hwoiz/ESPuino-JoliBox/Hardware-Plaforms/drill.jpg

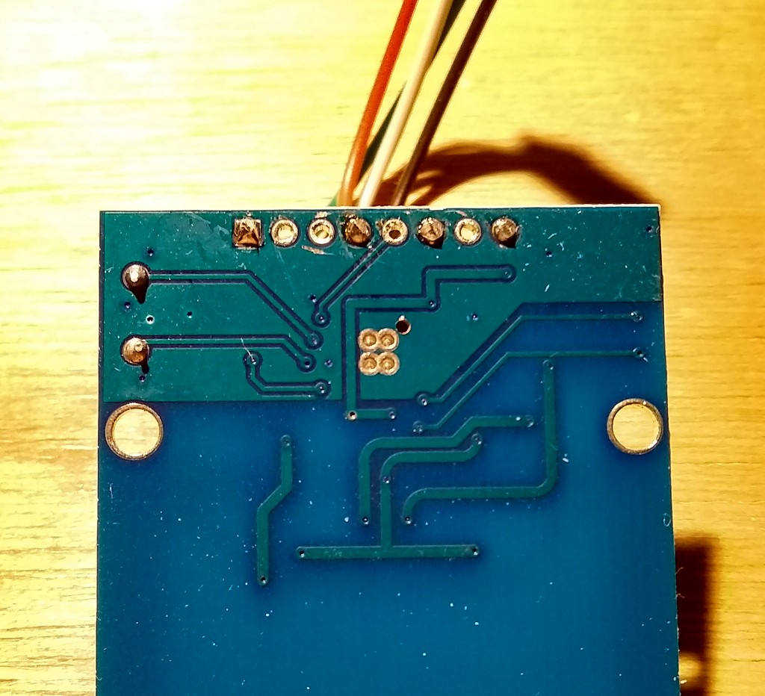
Hardware-Plaforms/drill.jpg
