hwoiz/ESPuino-JoliBox/Hardware-Plaforms/ESP32-A1S-Audiokit/docs/ESP32-A1S-Pinout.jpg

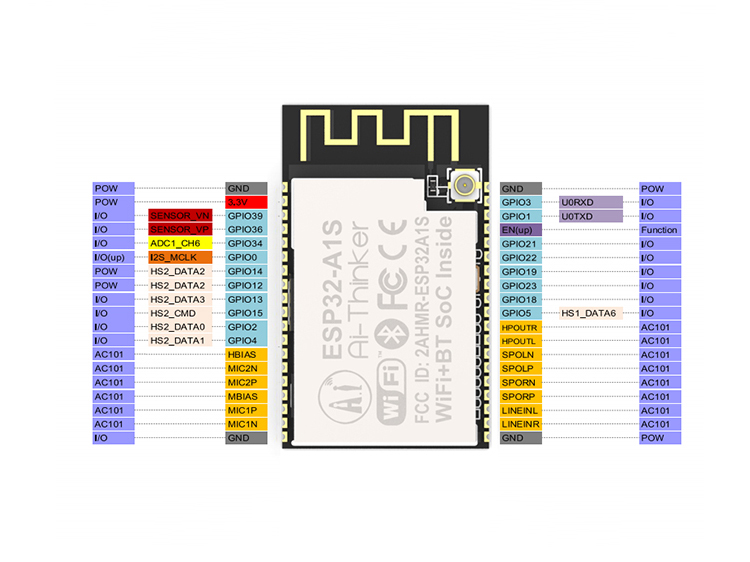
Hardware-Plaforms/ESP32-A1S-Audiokit/docs/ESP32-A1S-Pinout.jpg
