hwoiz/ESPuino-JoliBox/Hardware-Plaforms/ESP32-A1S-Audiokit/docs/ESP32-Audio-Kit2.2 ff.png

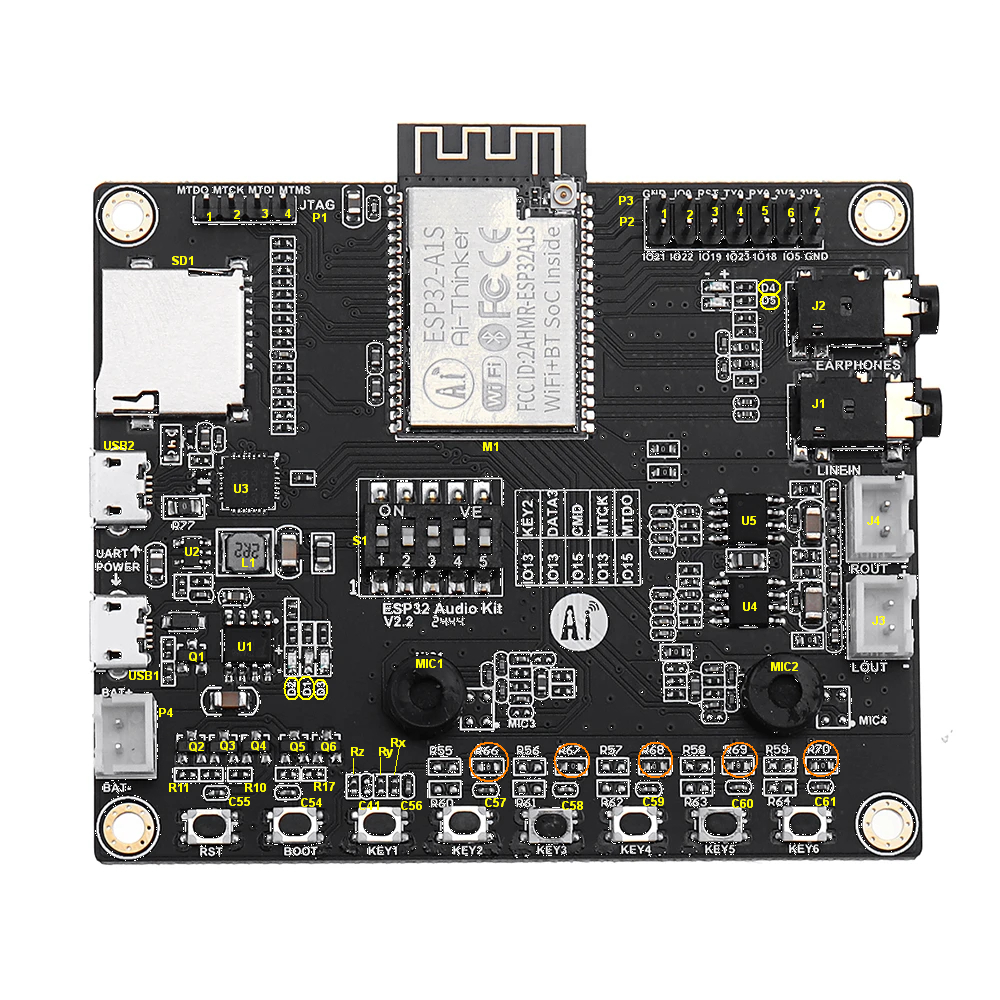
Hardware-Plaforms/ESP32-A1S-Audiokit/docs/ESP32-Audio-Kit2.2 ff.png
