hwoiz/ESPuino-JoliBox/Hardware-Plaforms/MRFC522-RC522-RFID.jpg

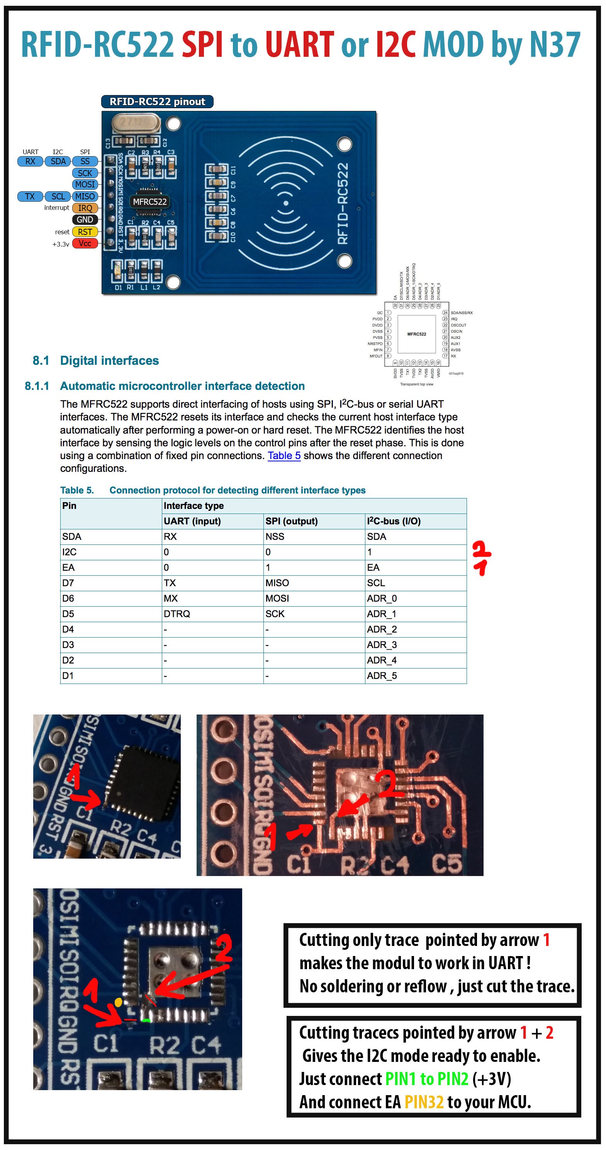
Hardware-Plaforms/MRFC522-RC522-RFID.jpg
