hwoiz/ESPuino-JoliBox/openHAB/pictures/openhab_overview.jpg

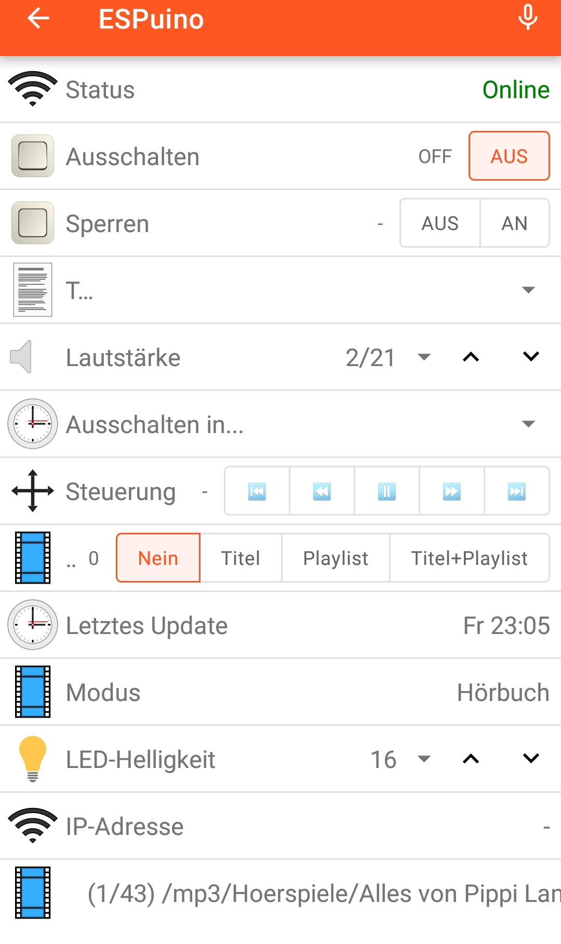
openHAB/pictures/openhab_overview.jpg
