hwoiz/ESPuino-JoliBox/openHAB/pictures/openhab_sleeping.jpg

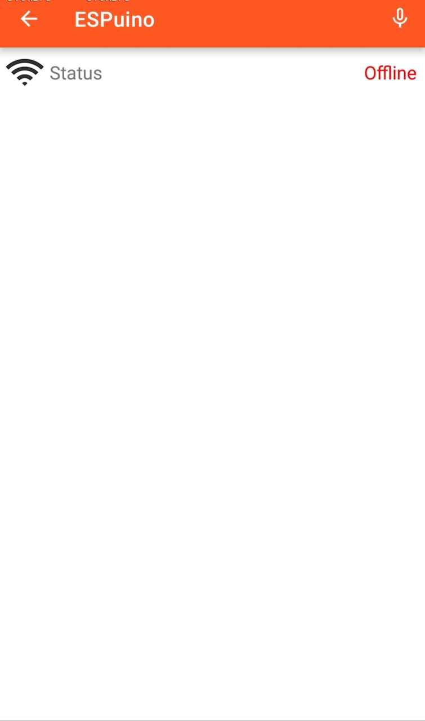
openHAB/pictures/openhab_sleeping.jpg
