hwoiz/ESPuino-JoliBox/openHAB/pictures/openhab_sleepTimer.jpg

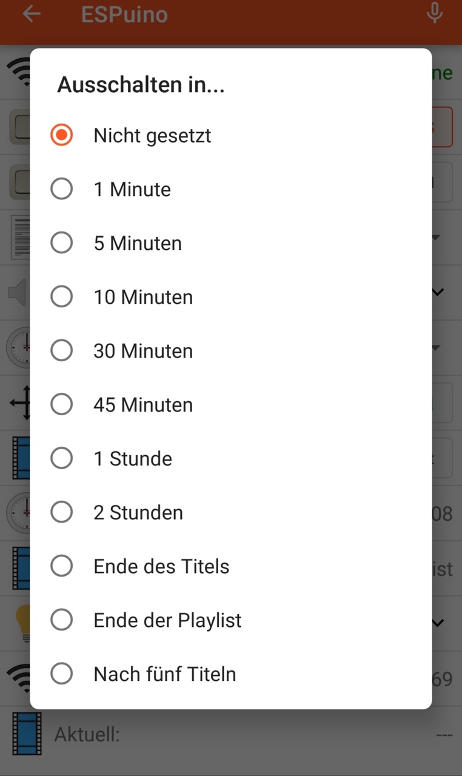
openHAB/pictures/openhab_sleepTimer.jpg
