hwoiz/ESPuino-JoliBox/openHAB/pictures/openhab_trackSelection.jpg

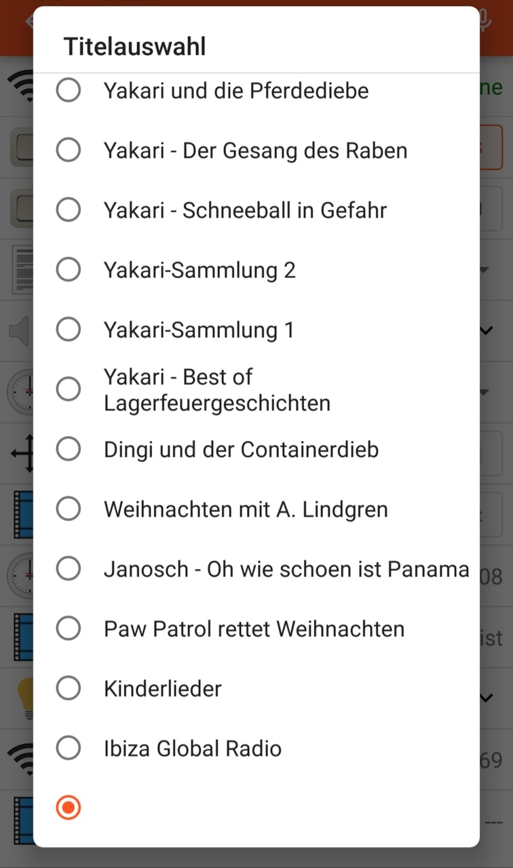
openHAB/pictures/openhab_trackSelection.jpg
