hwoiz/ESPuino-JoliBox/PCBs/AZDelivery_ESP32_NodeMCU/pictures/3d-model_front.png

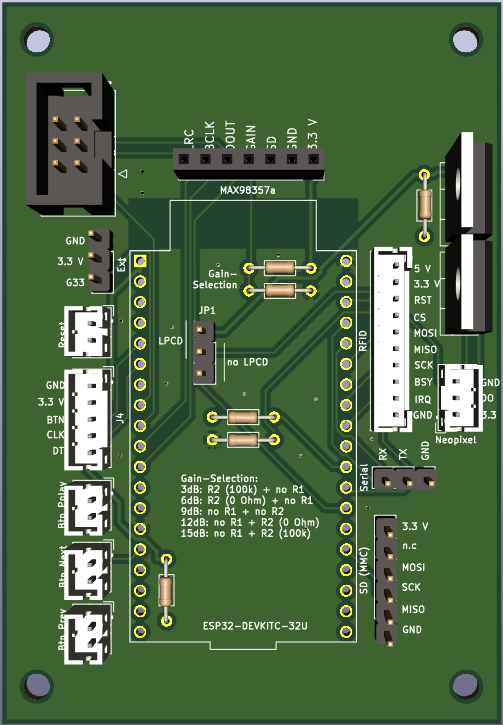
PCBs/AZDelivery_ESP32_NodeMCU/pictures/3d-model_front.png
