hwoiz/ESPuino-JoliBox/PCBs/Headphone with PCM5102a and TDA1308/Pictures/3D-model_downside.jpeg

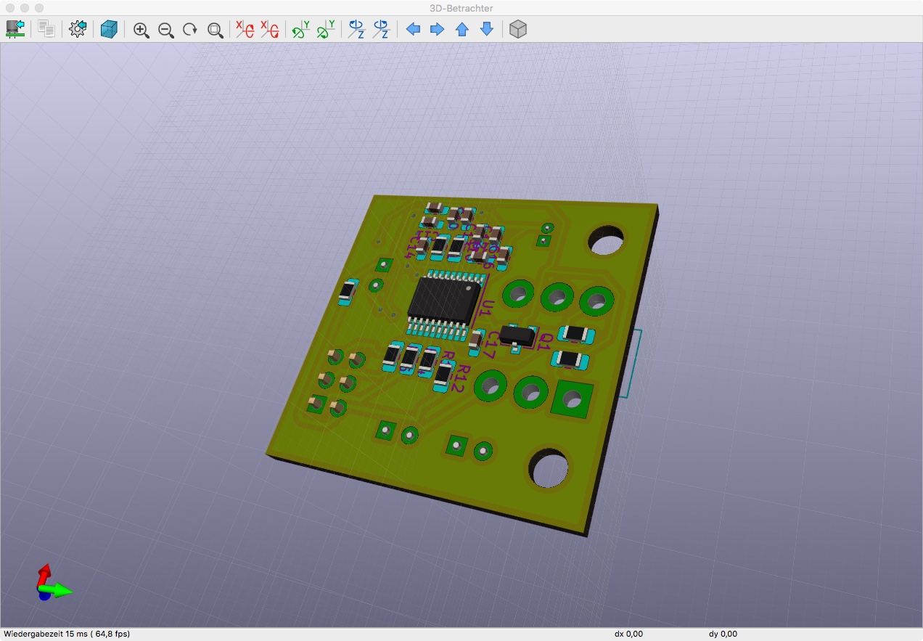
PCBs/Headphone with PCM5102a and TDA1308/Pictures/3D-model_downside.jpeg
