hwoiz/ESPuino-JoliBox/PCBs/Headphone with PCM5102a and TDA1308/Pictures/Headphone-pcb_upside.jpg

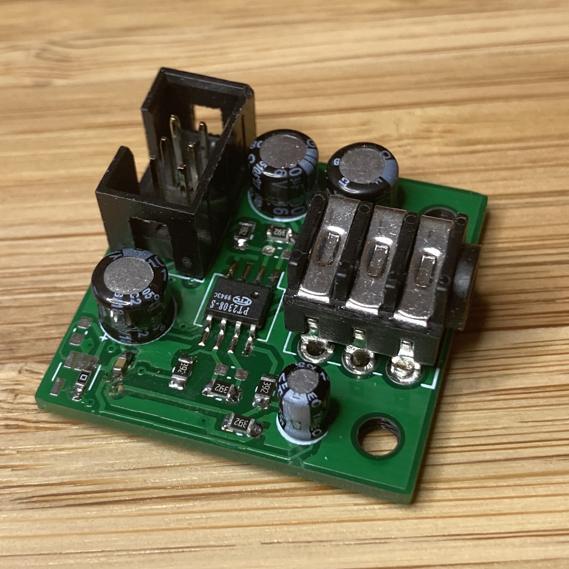
PCBs/Headphone with PCM5102a and TDA1308/Pictures/Headphone-pcb_upside.jpg
