hwoiz/ESPuino-JoliBox/PCBs/Wemos Lolin32 SD_MMC PN5180/Pictures/3d_Model_up.png

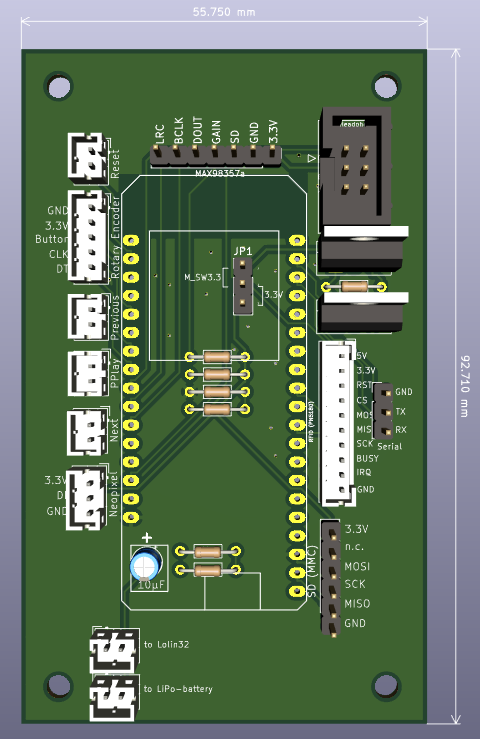
PCBs/Wemos Lolin32 SD_MMC PN5180/Pictures/3d_Model_up.png
