hwoiz/ESPuino-JoliBox/PCBs/Wemos Lolin32/Infos/LOLIN32_Circuit.png

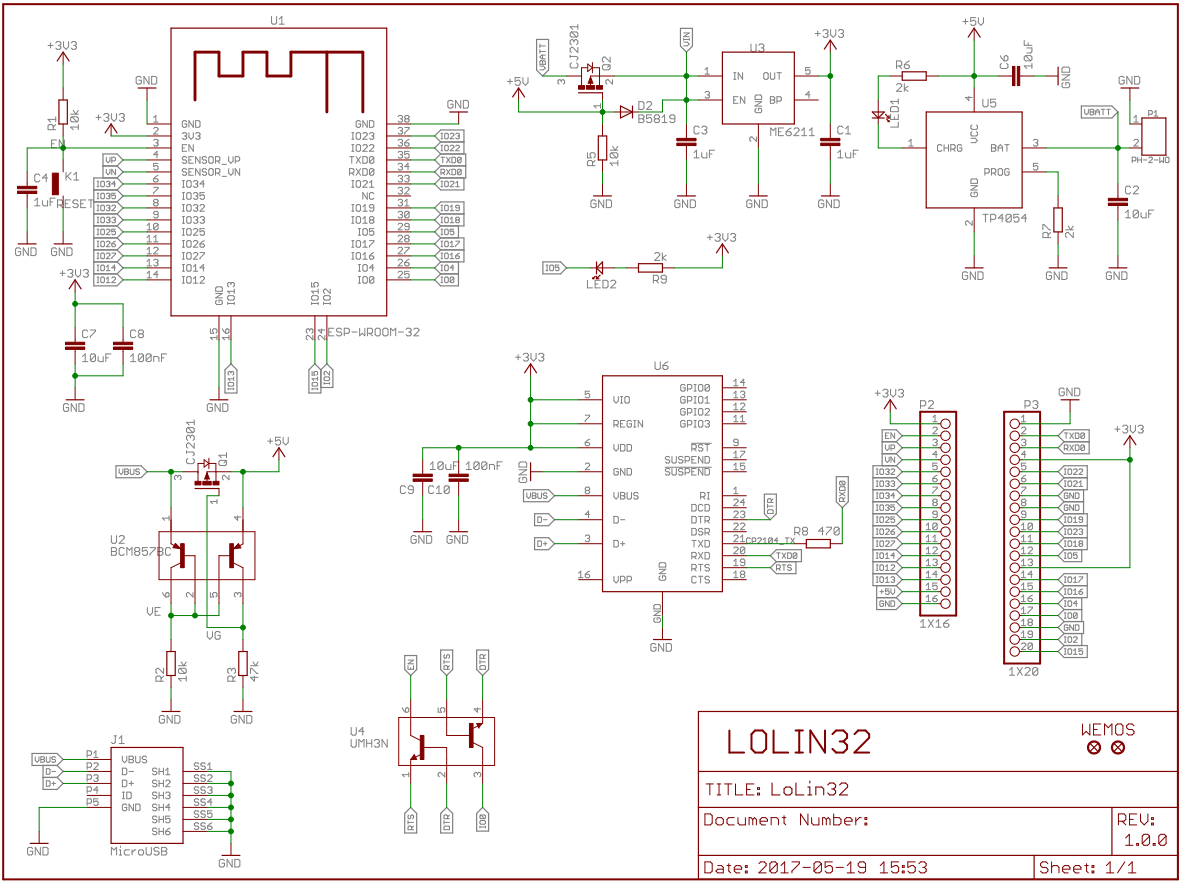
PCBs/Wemos Lolin32/Infos/LOLIN32_Circuit.png
