hwoiz/ESPuino-JoliBox/PCBs/Wemos Lolin32/Pictures/ESPuino V2_down.png

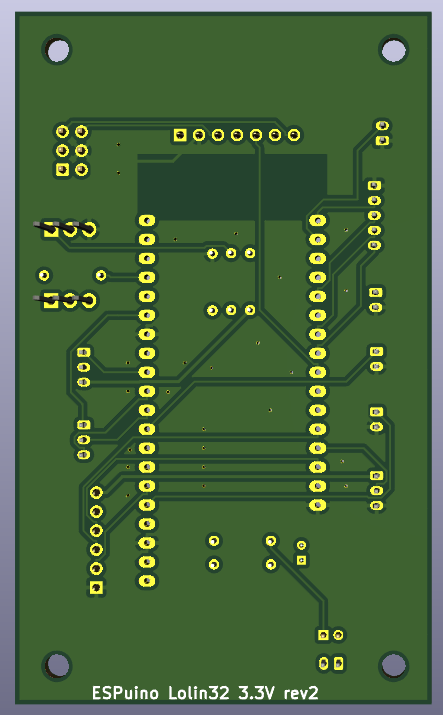
PCBs/Wemos Lolin32/Pictures/ESPuino V2_down.png
