hwoiz/ESPuino-JoliBox/PCBs/Wemos Lolin32/Pictures/ESPuino V2_up.png

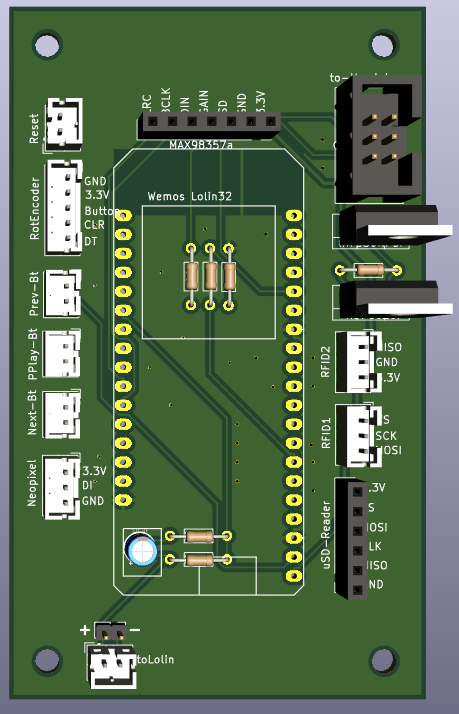
PCBs/Wemos Lolin32/Pictures/ESPuino V2_up.png
