hwoiz/ESPuino-JoliBox/PCBs/Wemos Lolin D32/Pictures/ESPuino D32_downside.png

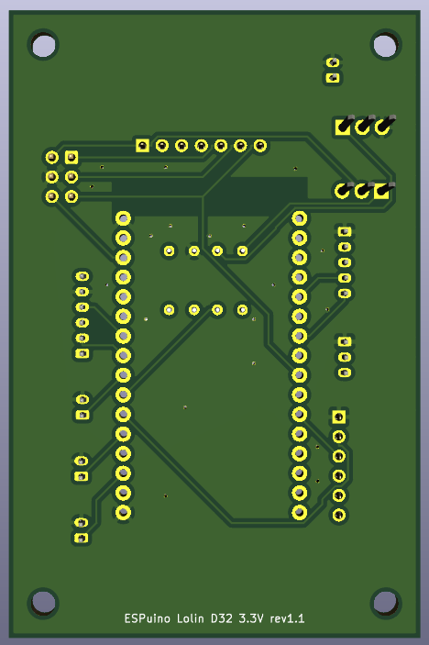
PCBs/Wemos Lolin D32/Pictures/ESPuino D32_downside.png
