hwoiz/ESPuino-JoliBox/PCBs/Wemos Lolin D32/Pictures/ESPuino D32_upside.png

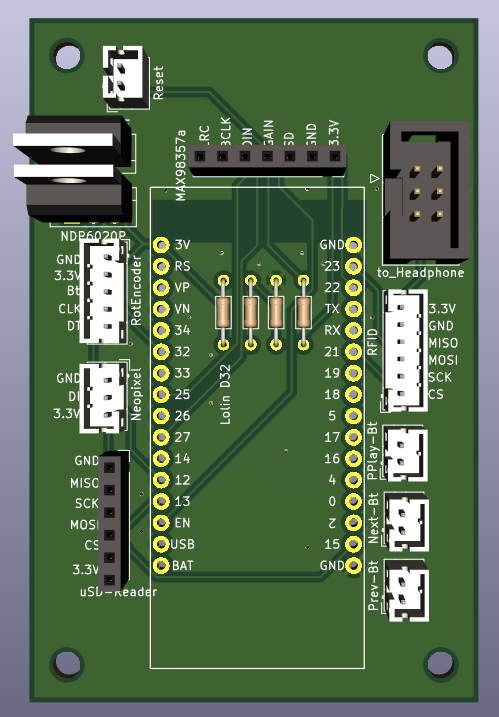
PCBs/Wemos Lolin D32/Pictures/ESPuino D32_upside.png
