hwoiz/ESPuino-JoliBox/pictures/Pullup-removal.jpg

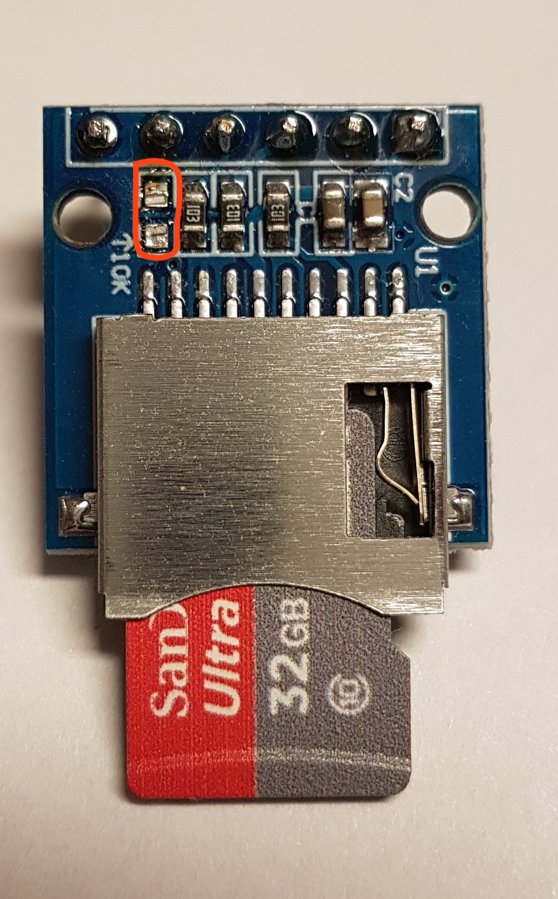
pictures/Pullup-removal.jpg
