hwoiz/ESPuino-JoliBox/PCBs/AZDelivery_ESP32_NodeMCU/pictures/Soldered_with_peripherals3.jpg

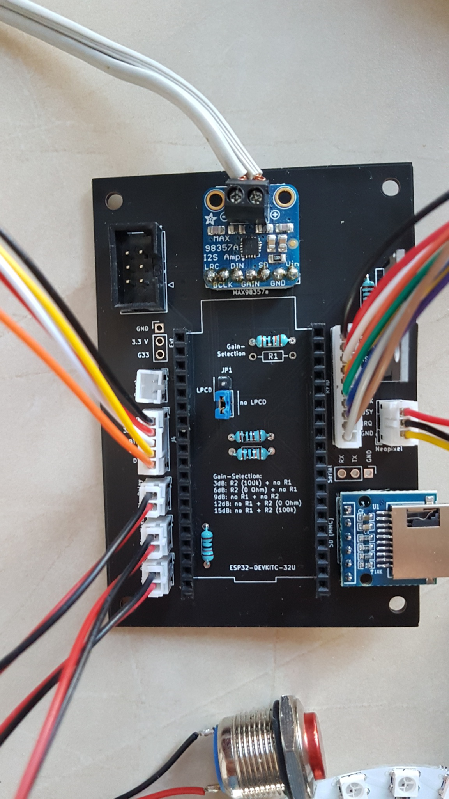
PCBs/AZDelivery_ESP32_NodeMCU/pictures/Soldered_with_peripherals3.jpg
