hwoiz/ESPuino-JoliBox/PCBs/Wemos Lolin32/Pictures/Soldered1_rev1.jpg

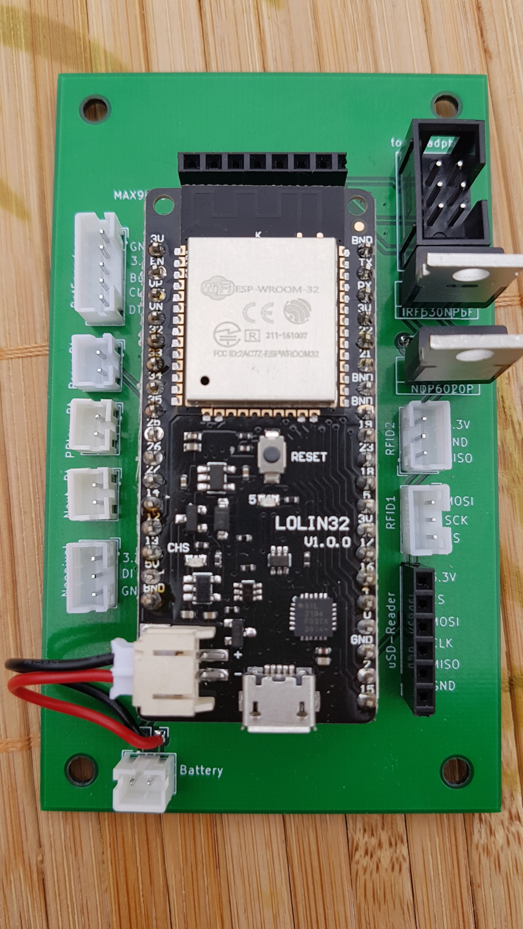
PCBs/Wemos Lolin32/Pictures/Soldered1_rev1.jpg
