hwoiz/ESPuino-JoliBox/PCBs/Wemos Lolin32/Pictures/Soldered2_rev1.jpg

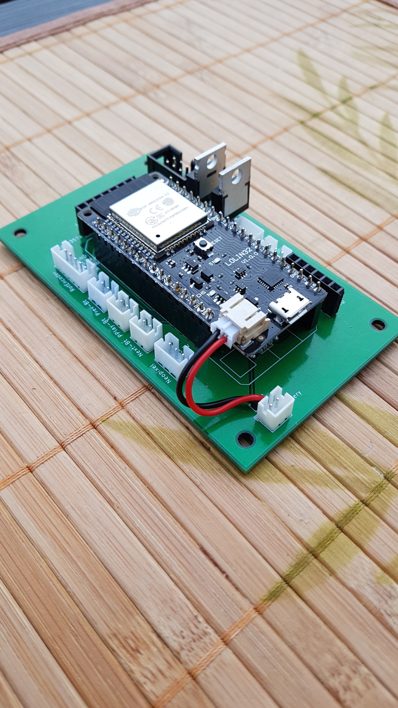
PCBs/Wemos Lolin32/Pictures/Soldered2_rev1.jpg
