hwoiz/ESPuino-JoliBox/PCBs/Wemos Lolin32/Pictures/Soldered with peripherals1_rev1.jpg

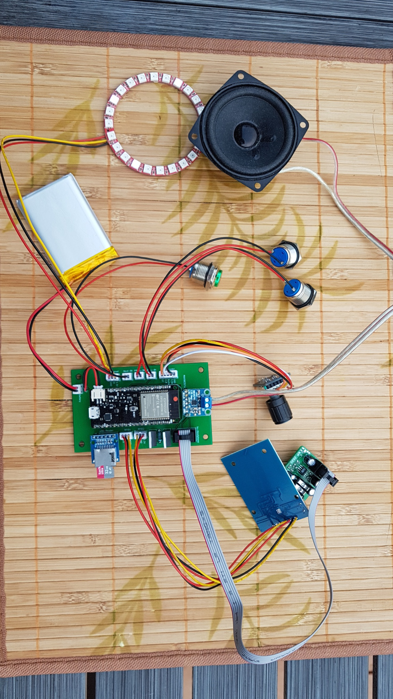
PCBs/Wemos Lolin32/Pictures/Soldered with peripherals1_rev1.jpg
