hwoiz/ESPuino-JoliBox/PCBs/Wemos Lolin32/Pictures/Soldered with peripherals2_rev1.jpg

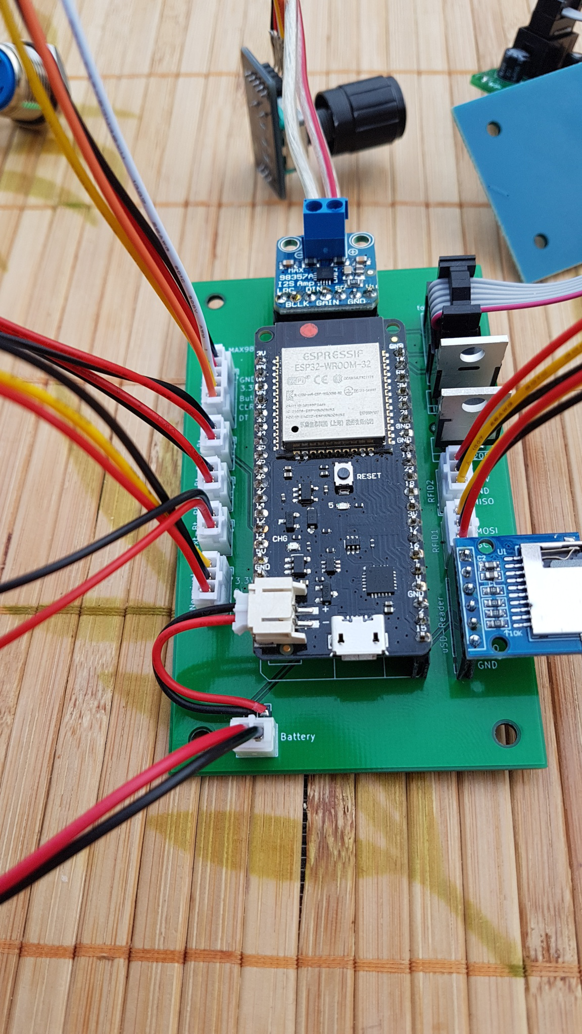
PCBs/Wemos Lolin32/Pictures/Soldered with peripherals2_rev1.jpg
