hwoiz/ESPuino-JoliBox/PCBs/Wemos Lolin D32/Pictures/Soldered 1.jpg

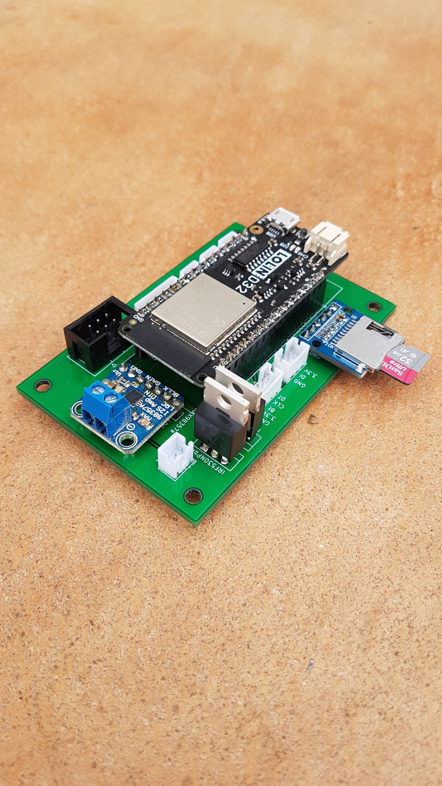
PCBs/Wemos Lolin D32/Pictures/Soldered 1.jpg
