hwoiz/ESPuino-JoliBox/PCBs/Wemos Lolin D32/Pictures/Soldered 2.jpg

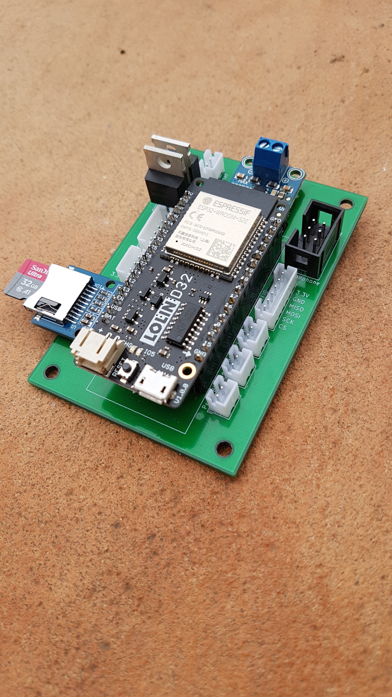
PCBs/Wemos Lolin D32/Pictures/Soldered 2.jpg
