hwoiz/ESPuino-JoliBox/PCBs/Wemos Lolin D32/Pictures/Soldered 3.jpg

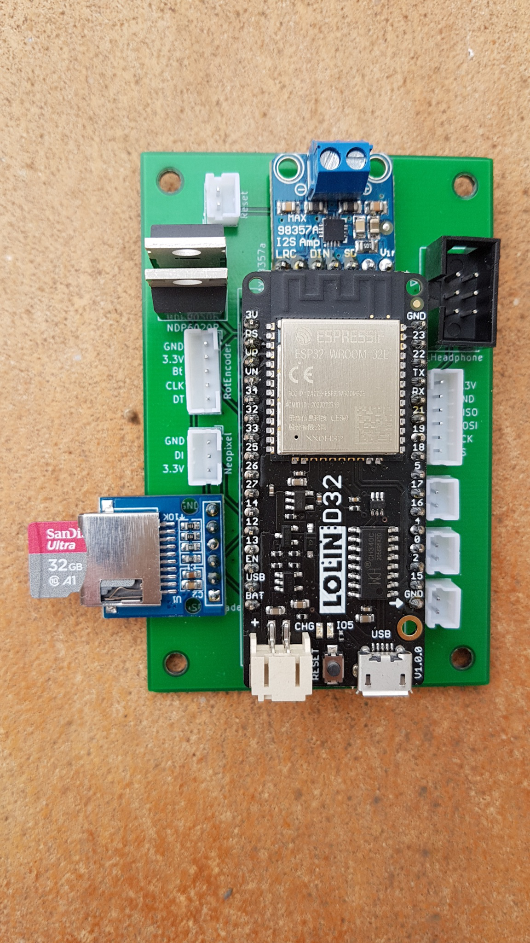
PCBs/Wemos Lolin D32/Pictures/Soldered 3.jpg
